hxelec/s3p/neopixel.ino

#include <Adafruit_NeoPixel.h>

#define PIN            21  // Define the pin to which the NeoPixel is connected
#define NUMPIXELS      1  // Number of NeoPixels in the strip

Adafruit_NeoPixel pixels = Adafruit_NeoPixel(NUMPIXELS, PIN, NEO_GRB + NEO_KHZ800);

void setup() {
  pixels.begin();  // Initialize the NeoPixel library
}

void loop() {
  rainbowCycle(20);  // Call the rainbowCycle function with a delay of 20 milliseconds
}

// Fill the dots one after the other with a color
void rainbowCycle(uint8_t wait) {
  uint16_t i, j;

  for(j=0; j<256*5; j++) { // 5 cycles of all colors on wheel
    for(i=0; i<pixels.numPixels(); i++) {
      pixels.setPixelColor(i, Wheel(((i * 256 / pixels.numPixels()) + j) & 255));
    }
    pixels.show();
    delay(wait);
  }
}

// Input a value 0 to 255 to get a color value.
// The colours are a transition r - g - b - back to r.
uint32_t Wheel(byte WheelPos) {
  WheelPos = 255 - WheelPos;
  if(WheelPos < 85) {
    return pixels.Color(255 - WheelPos * 3, 0, WheelPos * 3);
  }
  if(WheelPos < 170) {
    WheelPos -= 85;
    return pixels.Color(0, WheelPos * 3, 255 - WheelPos * 3);
  }
  WheelPos -= 170;
  return pixels.Color(WheelPos * 3, 255 - WheelPos * 3, 0);
}
